STGEW/TR_24_rc_car/resources/driver_connection.png

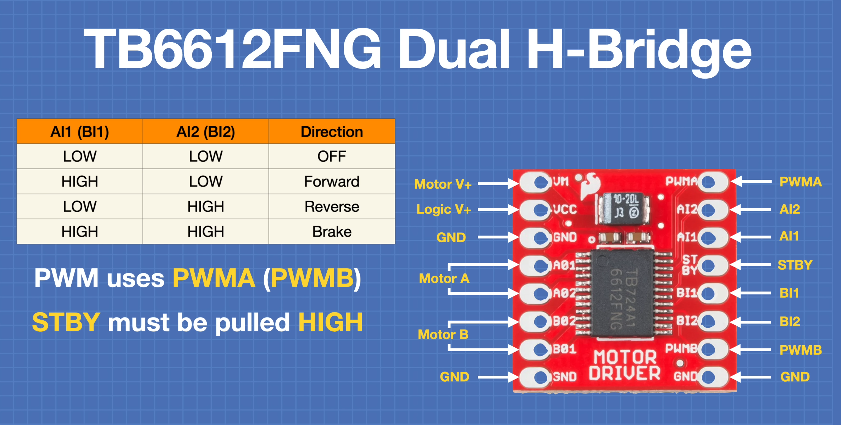
resources/driver_connection.png
