STGEW/TR_24_rc_car/resources/KY_023.jpg

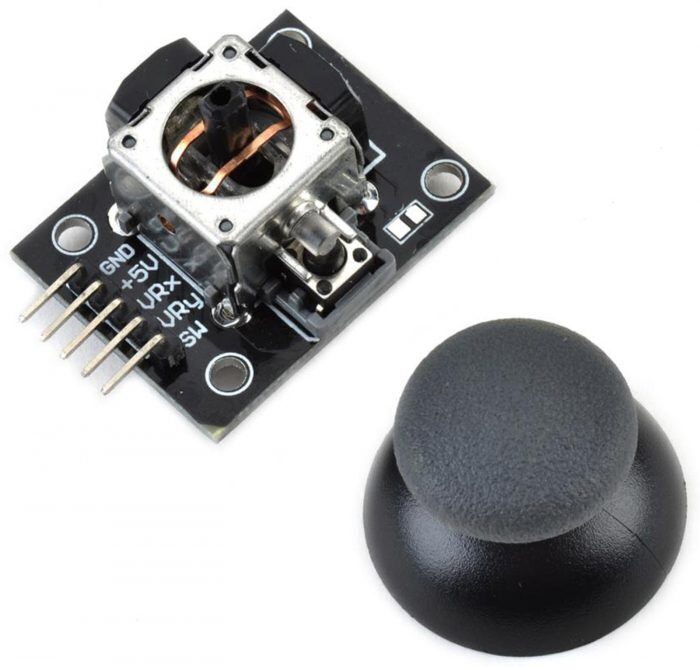
resources/KY_023.jpg
