STGEW/TR_24_rc_car/resources/led.jpg

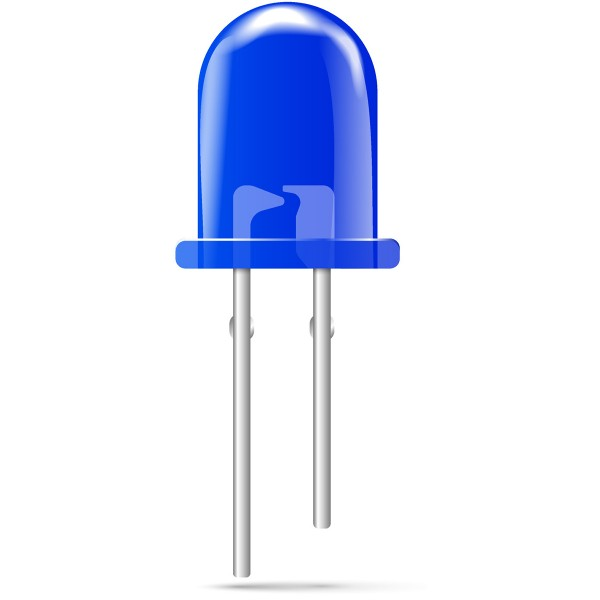
resources/led.jpg
