STGEW/TR_24_rc_car/freertos_code/car_MCU/cameraServoTask.h

#pragma once

#include "FreeRTOS.h"
#include "semphr.h"

// a semaphore to communicate with cameraAngle variable
extern SemaphoreHandle_t cameraServoSemaphore;
// an angle for camera to rotate
extern int cameraAngle;
