STGEW/TR_24_rc_car/freertos_code/rc_MCU/rfTxTask.cpp

#include "rfTxTask.h"
#include <stdio.h>
#include <RF24.h>
#include "../const.h"

// semaphore for reading data by commandsProcessor
SemaphoreHandle_t rfTxSemaphore;
struct JoystickRawData joystick = {0, 0, false};

RF24 radio(CE_PIN, CSN_PIN);
bool role = true; // true = TX role, false = RX role


void setupRfTxTask()
{
    // intially OFF
    gpio_init(RADIO_LED_PIN);
    gpio_set_dir(RADIO_LED_PIN, GPIO_OUT);
    gpio_put(RADIO_LED_PIN, 0);

    // Let these addresses be used for the pair
    uint8_t address[][6] = {"1Node", "2Node"};
    bool radioNumber = 0;

    // initialize the transceiver on the SPI bus
    if (!radio.begin()) {
        printf("radio hardware is not responding!!\n");
        return;
    }
    radio.setPALevel(RF24_PA_LOW); // RF24_PA_MAX is default.
    radio.setPayloadSize(sizeof(joystick)); // float datatype occupies 4 bytes
    radio.openWritingPipe(address[radioNumber]);
    radio.openReadingPipe(1, address[!radioNumber]); // using pipe 1
    radio.setChannel(124);
    radio.setDataRate(RF24_2MBPS);
    radio.setCRCLength(RF24_CRC_16);
    if (role) {
        radio.stopListening(); // put radio in TX mode
    }
    else {
        radio.startListening(); // put radio in RX mode
    }
}

void runRfTxTask( void *pvParameters )
{

    TickType_t xNextWakeTime;
    const unsigned long ulValueToSend = 100UL;

    /* Remove compiler warning about unused parameter. */
    ( void ) pvParameters;

    /* Initialise xNextWakeTime - this only needs to be done once. */
    xNextWakeTime = xTaskGetTickCount();
    TickType_t lastTXTicks = xTaskGetTickCount();
    TickType_t sinceLastTXTicks = 0;
    float sinceLastTXSec = 0.0;
    float lastToggleSec =  xTaskGetTickCount() / configTICK_RATE_HZ;

    for( ;; )
    {

        if (xSemaphoreTake(rfTxSemaphore, 0) == pdTRUE) {
            // printf(
            //     "joystick's values for processing are. x: %u, y: %u\n",
            //     joystick.x,
            //     joystick.y);

            bool report = radio.write(&joystick, sizeof(joystick));         // transmit & save the report
            if (report) {
                // printf("Transmission successful!\n");
                lastTXTicks = xTaskGetTickCount();
                if (joystick.ext_control == true) {
                    if (xTaskGetTickCount() / configTICK_RATE_HZ - lastToggleSec >= 1.0) {
                        // Switching LED state
                        gpio_xor_mask(1u << RADIO_LED_PIN);
                        lastToggleSec = xTaskGetTickCount() / configTICK_RATE_HZ;
                    }
                } else {
                    gpio_put(RADIO_LED_PIN, 1);
                }
                    
            }
            else {
                // printf("Transmission failed or timed out\n");
                sinceLastTXTicks = xTaskGetTickCount() - lastTXTicks;
                sinceLastTXSec = sinceLastTXTicks / configTICK_RATE_HZ;
                if (sinceLastTXSec > TX_LED_TIMEOUT_SEC) {
                    gpio_put(RADIO_LED_PIN, 0);
                }
            }

            xSemaphoreGive(rfTxSemaphore);

       } else {
           printf("RFTXTask didn't get a semaphore\n");
       }

        // 100 msec delay ~ 10 Hz
        vTaskDelay(pdMS_TO_TICKS( 10 ));
    }
}
