STGEW/TR_24_rc_car/freertos_code/car_MCU/enginesDataParser.h

#pragma once

#include <cstdint> // ??? Do I need it?
#include <cstddef> 
#include "../const.h"

#define body_size       sizeof(EnginesPwr)
#define header_size     sizeof(UART_ENGINES_DATA_HEADER)

enum ParserState {
    HEADER,
    BODY
};

class EnginesDataParser {

public:
    bool parse(const char symbol, EnginesPwr & e);

private:

    int compareCharArrays(const char arr1[2], const char arr2[2]);

    ParserState state = HEADER;
    size_t counter = 0;
    char header_buff[header_size];
    char body_buff[body_size];
};
