STGEW/TR_24_rc_car/freertos_code/rc_MCU/joystickTask.cpp

#include "FreeRTOS.h"
#include "pico/stdlib.h"
#include "hardware/adc.h"
#include "hardware/gpio.h"
#include <stdio.h>

#include "rfTxTask.h"
#include "../const.h"


void setupJoystickTask( void )
{
    // ADC input
    adc_init();
    adc_gpio_init(X_AXIS_PIN);
    adc_gpio_init(Y_AXIS_PIN);

    // btn to interrupt
    gpio_init(JOY_EXT_CTRL_PIN);
    gpio_set_dir(JOY_EXT_CTRL_PIN, GPIO_IN);
    gpio_pull_up(JOY_EXT_CTRL_PIN);
}


void runJoystickTask( void *pvParameters )
{

    TickType_t xNextWakeTime;
    const unsigned long ulValueToSend = 100UL;

    /* Remove compiler warning about unused parameter. */
    ( void ) pvParameters;

    /* Initialise xNextWakeTime - this only needs to be done once. */
    xNextWakeTime = xTaskGetTickCount();

    for( ;; )
    {
        // originally ADC returns values in range: 0 .. 4095
        adc_select_input(ADC_CHANNEL_X);
        joystick.x = adc_read();

        adc_select_input(ADC_CHANNEL_Y);
        joystick.y = adc_read();

        joystick.ext_control = gpio_get( JOY_EXT_CTRL_PIN );

        printf("joystick x: %d y: %d ext control: %s\n",
            joystick.x, joystick.y,
            joystick.ext_control ? "true" : "false");

        xSemaphoreGive(rfTxSemaphore);
        // 100 msec delay ~ 10 Hz
        vTaskDelay(pdMS_TO_TICKS( 10 ));
    }
}
